ampnics/4_channel_home_automation_PCB/Arbaa_Amp_V0.1/Docs/img2.png

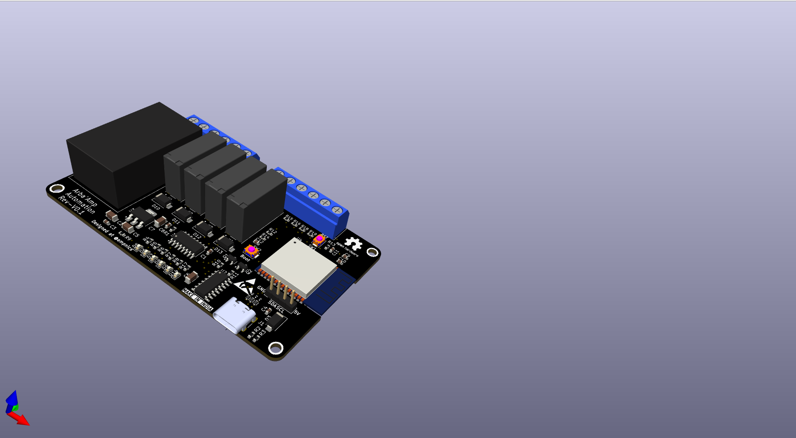
Arbaa_Amp_V0.1/Docs/img2.png
